AngryTroll/i8048_board/pcad/rev_A/photos/1_2.jpg

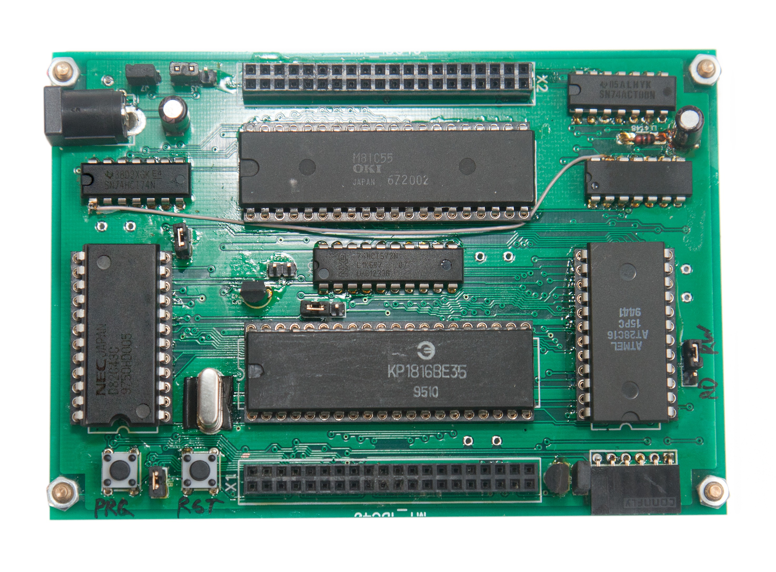
pcad/rev_A/photos/1_2.jpg
