AngryTroll/i8048_board/pcad/rev_A/photos/1_3.jpg

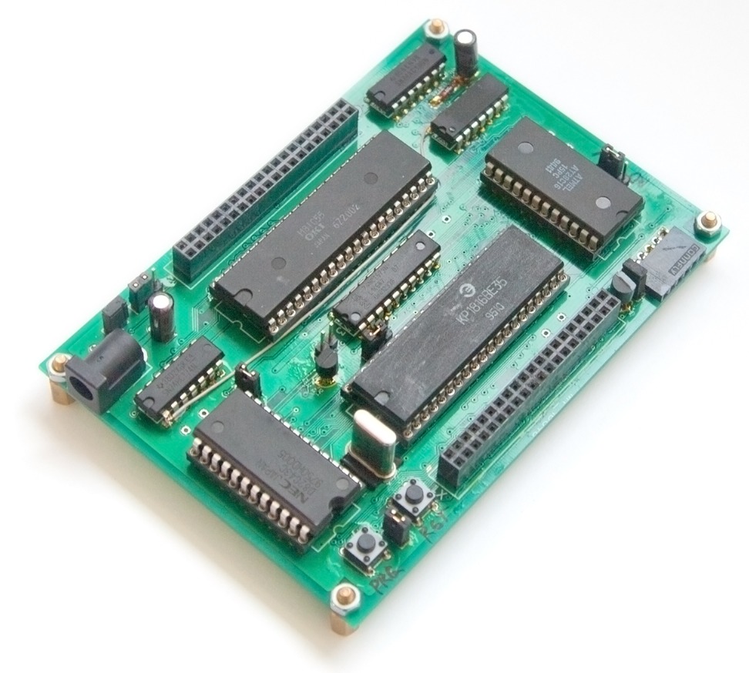
pcad/rev_A/photos/1_3.jpg
