AngryTroll/i8048_board/pcad/rev_A/photos/2_1.jpg

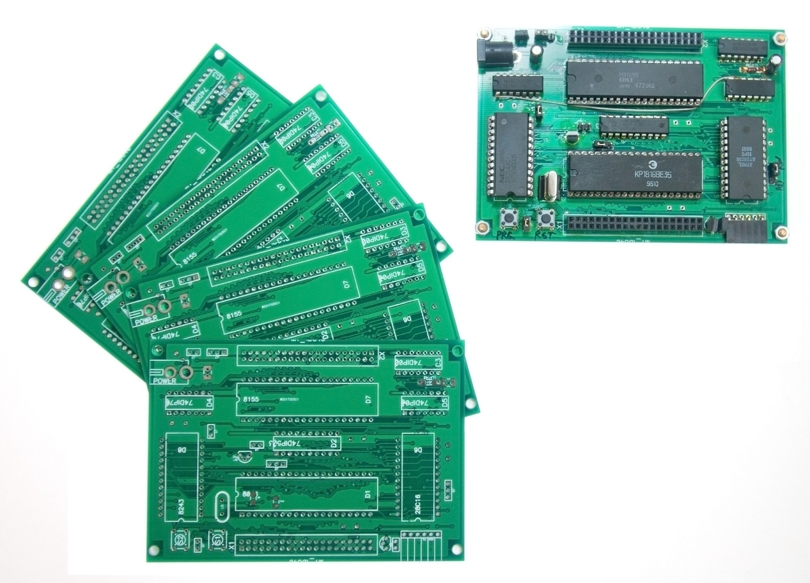
pcad/rev_A/photos/2_1.jpg
