AngryTroll/i8048_board/pcad/rev_A/photos/3_2.jpg

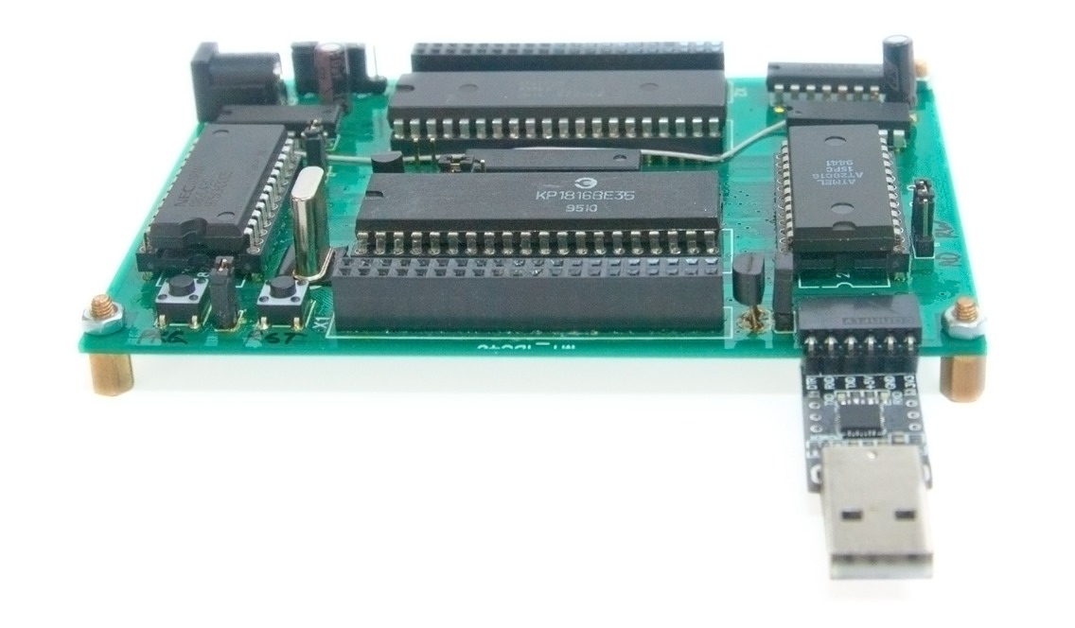
pcad/rev_A/photos/3_2.jpg
