AngryTroll/i8048_board/pcad/rev_A/photos/3_4.jpg

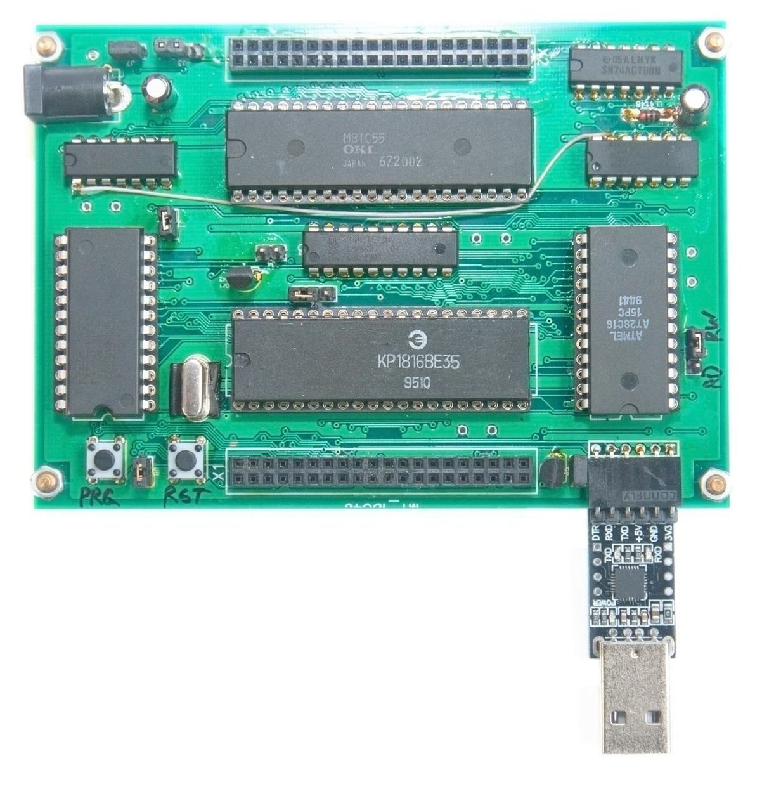
pcad/rev_A/photos/3_4.jpg
