AngryTroll/i8048_board/pcad/rev_A/i8048_board.pdf

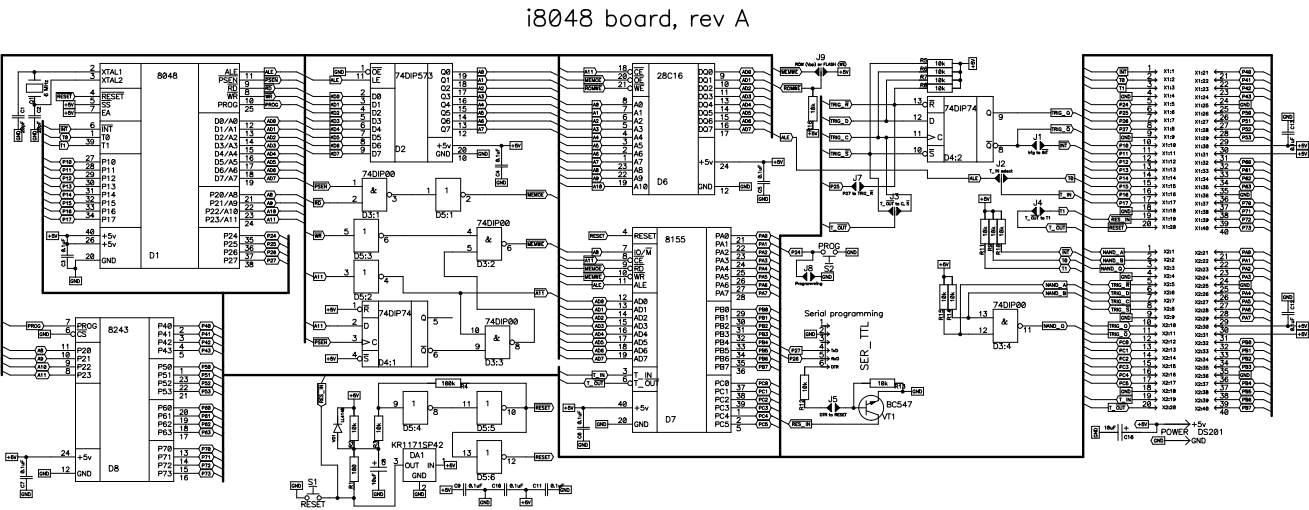
[picture p22: page 1]
